PixelCons/PixelCons-Frame/doc/img0.jpg

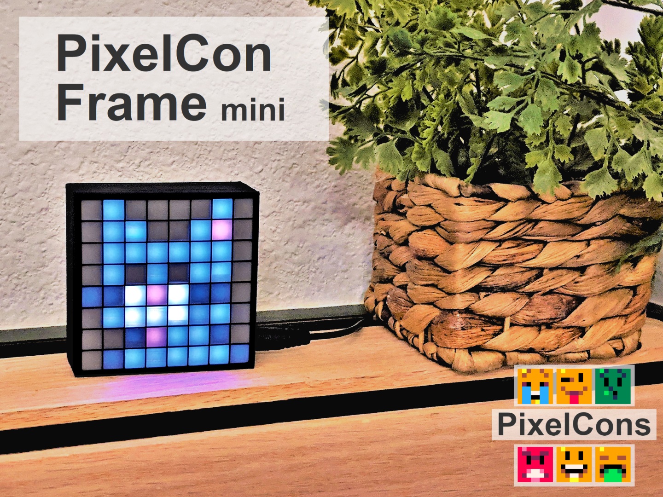
doc/img0.jpg
