PixelCons/PixelCons-Frame/doc/img2.jpg

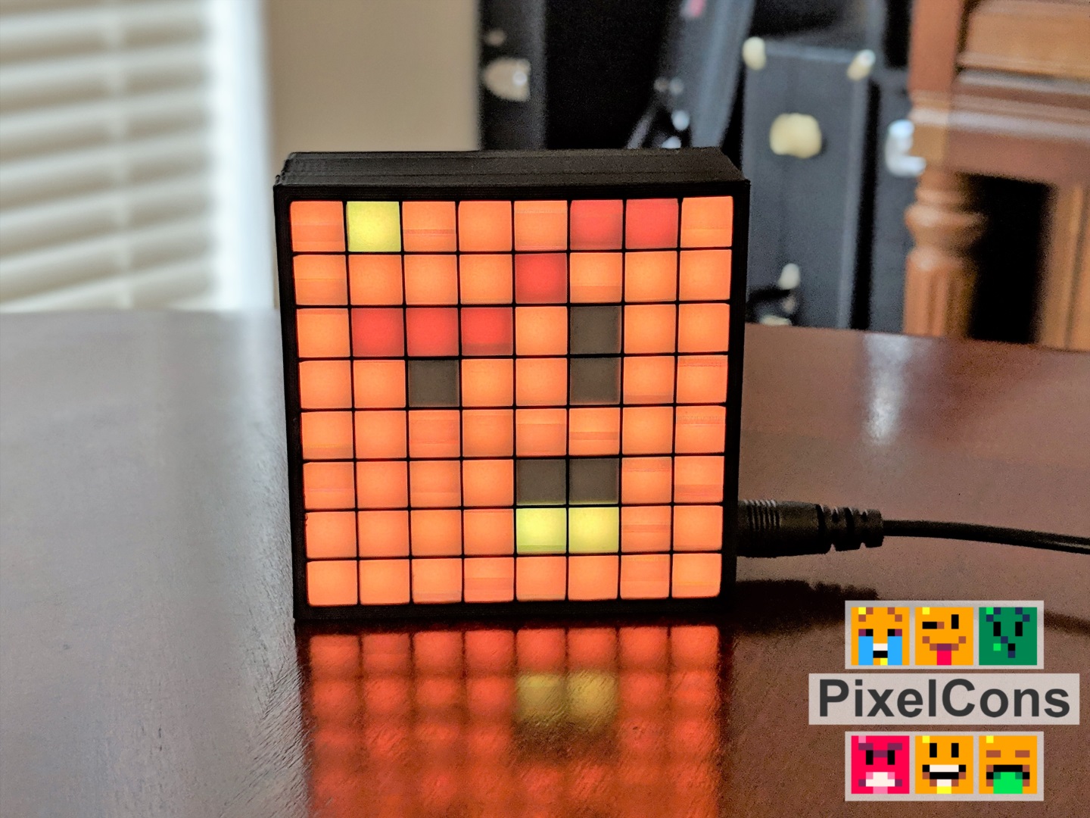
doc/img2.jpg
