PixelCons/PixelCons-Frame/doc/img3.jpg

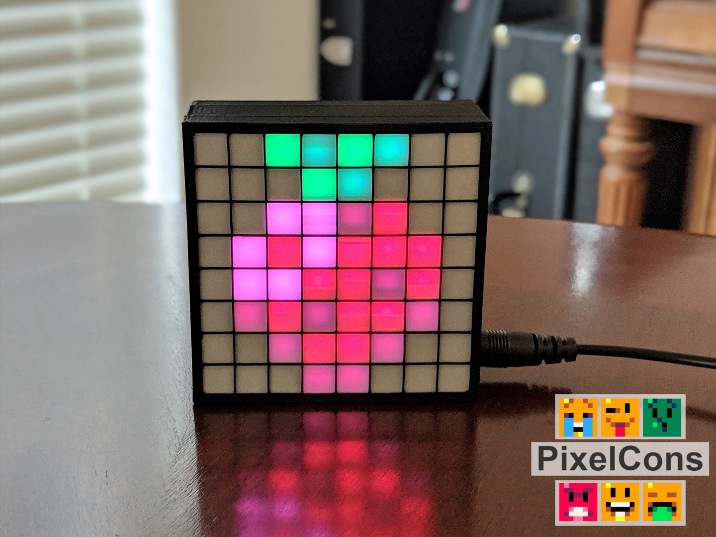
doc/img3.jpg
