PixelCons/PixelCons-Frame/doc/img4.jpg

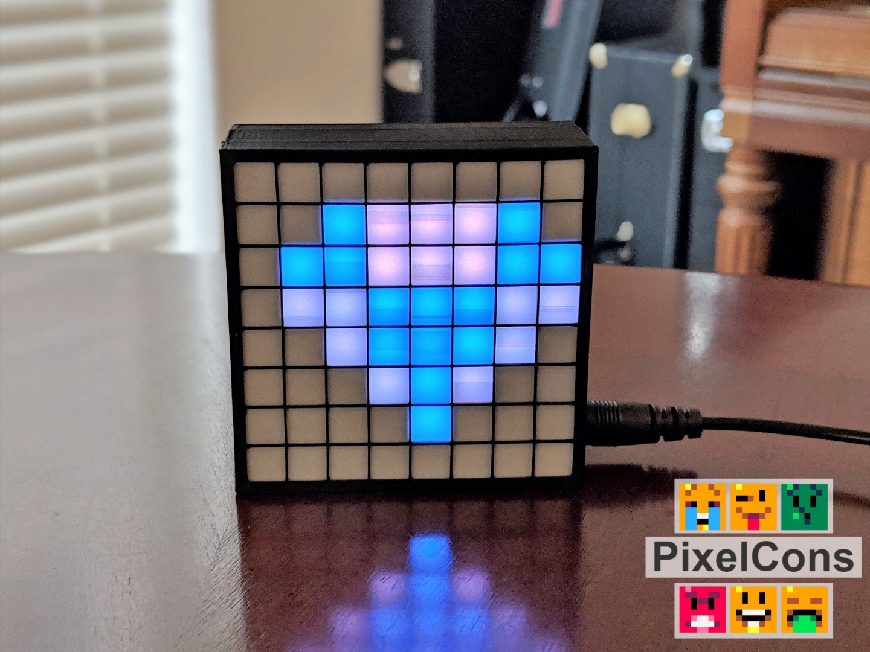
doc/img4.jpg
