PixelCons/PixelCons-Frame/doc/img6.jpg

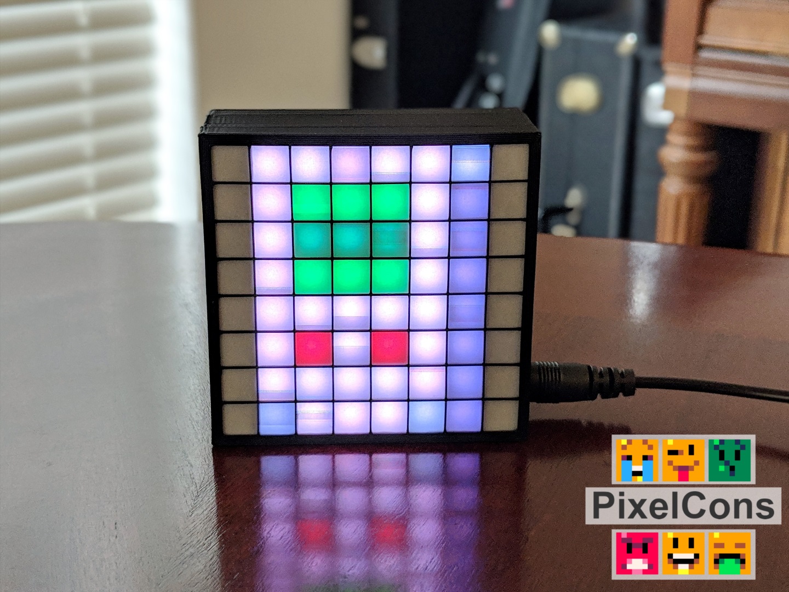
doc/img6.jpg
