PixelCons/PixelCons-Frame/src/storage.h

#ifndef STORAGE_H
#define STORAGE_H

#include <EEPROM.h>
#include "utils.h"

#define STORAGE_MAX_STATIC_PIXELCON 100
#define STORAGE_MAX_SOURCES 10
#define STORAGE_INIT_FLAG 159
	
namespace storage
{
	//////////////////////////////////////////////////////////////////////////////////////////////////////////////////////////
	///////////////////////////////////////////////////  Interface  //////////////////////////////////////////////////////////
	//////////////////////////////////////////////////////////////////////////////////////////////////////////////////////////
	void init();
	void commit();

	char getNumStaticPixelcon();
	void setNumStaticPixelcon(char num);

	void getStaticPixelconId(int index, char* pixelconId);
	uint8_t* getStaticPixelcon(int index);
	void setStaticPixelcon(int index, uint8_t* data);

	int getNumPixelconSources();

	char getPixelconSourceType(int index);
	void setPixelconSourceType(int index, char type);

	const char* getPixelconSourceId(int index);
	void setPixelconSourceId(int index, const char* id);

	bool getIsStaticMode();
	void setIsStaticMode(bool staticMode);
		
	char getBright();
	void setBright(char bright);
		
	int getDuration();
	void setDuration(int duration);
		
	const char* getRPCClient();
	void setRPCClient(const char* rpcClient);
	
	/* Helper Functions */
	void setDefaultStaticPixelconData(uint8_t* dataBuffer);
	
	
	/////////////////////////////////////////////////////////////////////////////////////////////////////////////////////
	///////////////////////////////////////////////////  Data  //////////////////////////////////////////////////////////
	/////////////////////////////////////////////////////////////////////////////////////////////////////////////////////
	const char numDefaultStaticPixelcon = 84;
	const char defaultStaticPixelcon[] PROGMEM = 
	  "9a999999990990999909909999999999907777099400004999477499999aa9999a9999999949949994944949ee9999eee499994e99400499999aa99999999999"
	  "9a9999999999909990049099999999999499994999400499999aa999999999999a99999999499499949449499999999991777719901dd10994777749999aa999"
	  "9a9999999949949c9494494c99999999907777099022220999088099999aa9999a99944999994999944490999909909999999999999900999999aa9999999999"
	  "9a999999990990999909909999999999994774999474474994499449999999999a9999999999999997099709977997799999999999422499999aa99999999999"
	  "9a9999999999999999099099990990999999999999422499949aa949999999999a99999999999099900490999999999994999949994224999998899999988999"
	  "9a99999994099049990990999999999992eeee29992882999997e999999999999a9999999949949994944949c999999c927777299428824999477499999aa999"
	  "9a999999994994999494494999999999949999499942249999988999999889999a9999999909909999099099999999999999a499999909999999a49999999999"
	  "9a9999999949949994944949ee9999eeee99a4ee999909999999a499999999999a99999999099099990990999c9999999c944999994aa4999999999999999999"
	  "9a499499949999499909909999099099999999999990099999900999999aa9999a9999999449944999999999900990099999999999900999999009999999c999"
	  "9a9999999449944999044099990990999999999999422499949aa949999999998e8888888228822888022088880880888888888888e77e8882777728888ee888"
	  "9a4994999499994999999999920990299cc99cc99cc77cc99cc00cc99cc9acc9cc1cc1ccc1cccc1cc77cc77c97099079977997799990099999900999999aa999"
	  "cc1cc1ccc1cccc1ccc0cc0cc990990999c9999999c99999999900999999aa9993b1331333133331333033033330330333331333333b303333333133333333333"
	  "9a99999999999999944994499999999994000049903bb30994bbbb4999bbbb999a99999999999999977997099079977999999999990099099099009999999999"
	  "0d0000d00dd00de00dddddd00d0d0dd0117e71100d777dd0001edd1001ddddd100999900099999909949090499499f229909ffff0044ffff049940e0499ff400"
	  "00028000028880000027770004970700004977700002877000028777000d777711111110111fffe000010010fdf00e00ffffff200effeee00e2fffe00ee22000"
	  "03bbbb303b7bbbb3b3bbbb3bb70bb70bb30bb03b0bbbbbb000b33b00000bb0000dccccd0dc7ccccdcdccccdcc70cc70ccd0cc0dc0cccccc000cddc00000cc000"
	  "00088270008822000777666006eeeed0f72fe26ef7f76e6e067e26d000676d00ff4444fff467764f46b33b64673703766730037647b33b7efe7777efffffffff"
	  "ff4444fff467764f46dccd6467c70c7667c00c7647dccd7efe7777efffffffff00b3b300000b300000ee28000e8e88800ee88280028288200028820000022000"
	  "00000000070000700cd66dc006d77d600d622dd001688d1000d6d10000000000001282100128a811128a988228aaaaa88aaaaa822889a821118a821001282100"
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
	/////////////////////////////////////////////////////////////////////////////////////////////////////////////////////
	void init() {
	  EEPROM.begin(3968);
	  EEPROM.get(0, flashData);
	  EEPROM.end();

	  // initialize flash data if it hasn't been set yet
	  if(flashData.initCheck != STORAGE_INIT_FLAG) {
		flashData.initCheck = STORAGE_INIT_FLAG;
		flashData.staticMode = 0;
		flashData.numStaticPixelcons = numDefaultStaticPixelcon;
		setDefaultStaticPixelconData(flashData.staticPixelconData);
		for(int i=0; i<STORAGE_MAX_SOURCES; i++) {
		  flashData.sourceTypes[i] = 0;
		  flashData.sourceIds[i][0] = 0;
		}
		flashData.sourceTypes[0] = 1;
		memset((char*)flashData.sourceIds[0], 0, 41);
		strcpy((char*)flashData.sourceIds[0], "f88e77f202db096e75596b468eef7c16282156b1");
		memset((char*)flashData.rpcClient, 0, 256);
		strcpy((char*)flashData.rpcClient, "mainnet.infura.io/v3/07d72fe8b8b74534a05d2091e108e26e");
		flashData.brightness = 80;
		flashData.duration = 30;
		commit(); 
	  }
	}

	void commit() {
	  EEPROM.begin(3968);
	  EEPROM.put(0, flashData);
	  EEPROM.commit(); 
	  EEPROM.end();
	}
	
	void setDefaultStaticPixelconData(uint8_t* dataBuffer) {
	  for(int i=0; i<numDefaultStaticPixelcon*32; i++) {
		int defaultDataIndex = i*2;
		uint8_t upperValue = toVal(pgm_read_byte_near(defaultStaticPixelcon + defaultDataIndex));
		uint8_t lowerValue = toVal(pgm_read_byte_near(defaultStaticPixelcon + defaultDataIndex + 1));
		dataBuffer[i] = (upperValue << 4) + lowerValue;
	  }
	}

	char getNumStaticPixelcon() {
	  return flashData.numStaticPixelcons;
	}
	
	void setNumStaticPixelcon(char num) {
	  flashData.numStaticPixelcons = num;
	}

	void getStaticPixelconId(int index, char* pixelconId) {
	  for(int i=0; i<32; i++) {
		uint8_t value = flashData.staticPixelconData[32*index + i];
		int stringIndex = i*2;
		pixelconId[stringIndex+0] = toHex((value & 0xF0) >> 4);
		pixelconId[stringIndex+1] = toHex(value & 0x0F);
	  }
	}
	
	uint8_t* getStaticPixelcon(int index) {
	  return &(flashData.staticPixelconData[32*index]);
	}
	
	void setStaticPixelcon(int index, uint8_t* data) {
	  int startIndex = 32*index;
	  for(int i=0; i<32; i++) flashData.staticPixelconData[startIndex+i] = data[i];
	}

	int getNumPixelconSources() {
	  int count = 0;
	  while(count < STORAGE_MAX_SOURCES) {
		if(flashData.sourceTypes[count] > 0) count++;
		else break;
	  }
	  return count;
	}

	char getPixelconSourceType(int index) {
	  return flashData.sourceTypes[index];
	}
	
	void setPixelconSourceType(int index, char type) {
	  flashData.sourceTypes[index] = type;
	}

	const char* getPixelconSourceId(int index) {
	  return (char*)flashData.sourceIds[index];
	}
	
	void setPixelconSourceId(int index, const char* id) {
	  memset((char*)flashData.sourceIds[index], 0, 41);
	  strcpy((char*)flashData.sourceIds[index], id);
	}

	bool getIsStaticMode() {
	  return flashData.staticMode > 0;
	}
	
	void setIsStaticMode(bool staticMode) {
	  if(staticMode) flashData.staticMode = 1;
	  else flashData.staticMode = 0;
	}

	char getBright() {
	  return flashData.brightness;
	}
	
	void setBright(char bright) {
	  flashData.brightness = bright;
	}

	int getDuration() {
	  return flashData.duration;
	}
	
	void setDuration(int duration) {
	  flashData.duration = duration;
	}

	const char* getRPCClient() {
	  return (const char*)flashData.rpcClient;
	}
	
	void setRPCClient(const char* rpcClient) {
	  memset((char*)flashData.rpcClient, 0, 256);
	  strcpy((char*)flashData.rpcClient, rpcClient);
	}
	
	
}

#endif /* STORAGE_H */
